un4ckn0wl3z/WiFi_Frauder_DEV/src/functions.cpp

// functions.cpp
#include "main.h"

bool readSSIDList() {
    File file = SPIFFS.open("/funny_ssid_list.txt", "r");
    if (!file) {
        Serial.println(F("Failed to open funny_ssid_list.txt"));
        return false;
    }

    custom_ssid_count = 0;
    while (file.available() && custom_ssid_count < 64) {
        String line = file.readStringUntil('\n');
        line.trim();
        if (line.length() > 0) {
            custom_ssids[custom_ssid_count] = line;
            custom_ssid_count++;
        }
    }
    file.close();
    return custom_ssid_count > 0;
}

void displayLogoAnimation() {
    // Slide logo up from bottom to top
    for (int y = 0; y <= 64; y += 1) {
        display.clearDisplay();
        display.drawBitmap(0, y, DEVIL_LOGO, 128, 64, SSD1306_WHITE);
        display.display();
    }
    // Slide logo down from top to final position
    for (int y = 64; y >= 0; y -= 1) {
        display.clearDisplay();
        display.drawBitmap(0, y, DEVIL_LOGO, 128, 64, SSD1306_WHITE);
        display.display();
    }
    // Display final logo position
    display.clearDisplay();
    display.drawBitmap(0, 0, DEVIL_LOGO, 128, 64, SSD1306_WHITE);
    display.display();
    vTaskDelay(2000 / portTICK_PERIOD_MS);
}

String generateRandomSSID() {
    const char chars[] = "ABCDEFGHIJKLMNOPQRSTUVWXYZ0123456789";
    String ssid = "";
    for (int i = 0; i < 8; i++) {
        ssid += chars[random(0, strlen(chars))];
    }
    return ssid;
}

// Updated displayTask to handle scrolling
void displayTask(void *pvParameters) {
    while (1) {
        if (menu_active) {
            display.clearDisplay();
            display.setTextSize(1);
            display.setTextColor(SSD1306_WHITE);

            // Display up to max_display_items menu items
            for (int i = 0; i < max_display_items; i++) {
                int menu_index = display_start + i;
                if (menu_index >= menu_item_count) break; // Stop if we reach the end of the menu

                // Highlight the selected item
                if (menu_index == current_menu) {
                    display.setTextColor(SSD1306_BLACK, SSD1306_WHITE); // Inverted for highlight
                    display.setCursor(0, 10 + i * 12);
                    display.print("> ");
                    display.println(menu_items[menu_index]);
                    display.setTextColor(SSD1306_WHITE); // Reset to normal
                } else {
                    display.setCursor(0, 10 + i * 12);
                    display.print("  ");
                    display.println(menu_items[menu_index]);
                }
            }

            // Optional: Add scroll indicators
            if (display_start > 0) {
                display.setCursor(120, 0);
                display.print("^"); // Up arrow
            }
            if (display_start + max_display_items < menu_item_count) {
                display.setCursor(120, 56);
                display.print("v"); // Down arrow
            }

            display.display();
        }
        vTaskDelay(100 / portTICK_PERIOD_MS); // Update every 100ms
    }
}
void spamRandomSSIDSlow(void *pvParameters) {
    spamming = true;
    WiFi.softAP("InitialSSID"); // Initialize AP
    while (spamming) {
        String ssid = generateRandomSSID();
        WiFi.softAP(ssid.c_str(), NULL, random(1, 12));
        display.clearDisplay();
        display.setTextSize(1);
        display.setTextColor(SSD1306_WHITE);
        display.setCursor(20, 20);
        display.println(F("Random SSID (Slow)"));
        display.setCursor(20, 40);
        display.println(ssid);
        display.display();
        vTaskDelay(1000 / portTICK_PERIOD_MS);
    }
    WiFi.softAPdisconnect(true);
    vTaskDelete(NULL);
}

void spamCustomSSID(void *pvParameters) {
    spamming = true;
    WiFi.softAP("InitialSSID"); // Initialize AP
    if (custom_ssid_count == 0) {
        display.clearDisplay();
        display.setTextSize(1);
        display.setTextColor(SSD1306_WHITE);
        display.setCursor(10, 20);
        display.println(F("No SSIDs in funny_ssid_list.txt"));
        display.display();
        vTaskDelay(2000 / portTICK_PERIOD_MS);
        spamming = false;
        menu_active = true;
        WiFi.softAPdisconnect(true);
        vTaskDelete(NULL);
        return;
    }
    while (spamming) {
        for (int i = 0; i < custom_ssid_count; i++) {
            if (!spamming) break;
            WiFi.softAP(custom_ssids[i].c_str(), NULL, random(1, 12));
            display.clearDisplay();
            display.setTextSize(1);
            display.setTextColor(SSD1306_WHITE);
            display.setCursor(10, 20);
            display.println(F("Custom SSID Spam"));
            display.setCursor(10, 40);
            display.println(custom_ssids[i]);
            display.display();
            vTaskDelay(100 / portTICK_PERIOD_MS);
        }
    }
    WiFi.softAPdisconnect(true);
    vTaskDelete(NULL);
}

void spamRandomSSIDFast(void *pvParameters) {
    spamming = true;
    WiFi.softAP("InitialSSID"); // Initialize AP
    while (spamming) {
        for (int i = 0; i < num_ssids; i++) {
            if (!spamming) break;
            WiFi.softAP(ssids[i].c_str(), NULL, random(1, 12));
            display.clearDisplay();
            display.setTextSize(1);
            display.setTextColor(SSD1306_WHITE);
            display.setCursor(10, 20);
            display.println(F("Random SSID (Fast)"));
            display.setCursor(10, 40);
            display.println(ssids[i]);
            display.display();
            vTaskDelay(100 / portTICK_PERIOD_MS);
        }
    }
    WiFi.softAPdisconnect(true);
    vTaskDelete(NULL);
}
